mend0z0/SparkleSplashy/Hardware/v1_20230102/Released Files/Source Files/3D Parts/User Library-XFDFN-8E.step

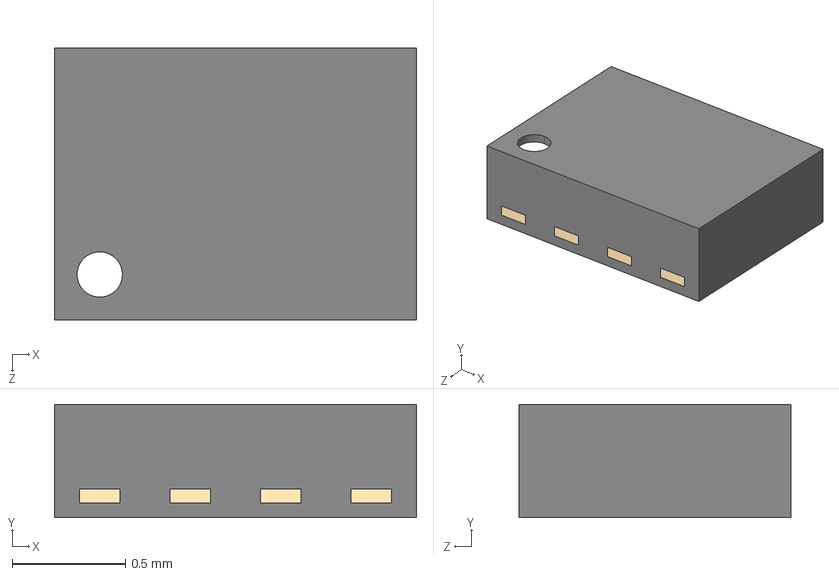
[picture p17: CAD file, 2023-09-30]
Hardware/v1_20230102/Released Files/Source Files/3D Parts/User Library-XFDFN-8E.step
1.60 x 0.5 x 1.20 mm
