mend0z0/SparkleSplashy/Hardware/v1_20230102/Design Files/_HW_SparkleSplashy/3D Parts/User Library-DO-214BA.step

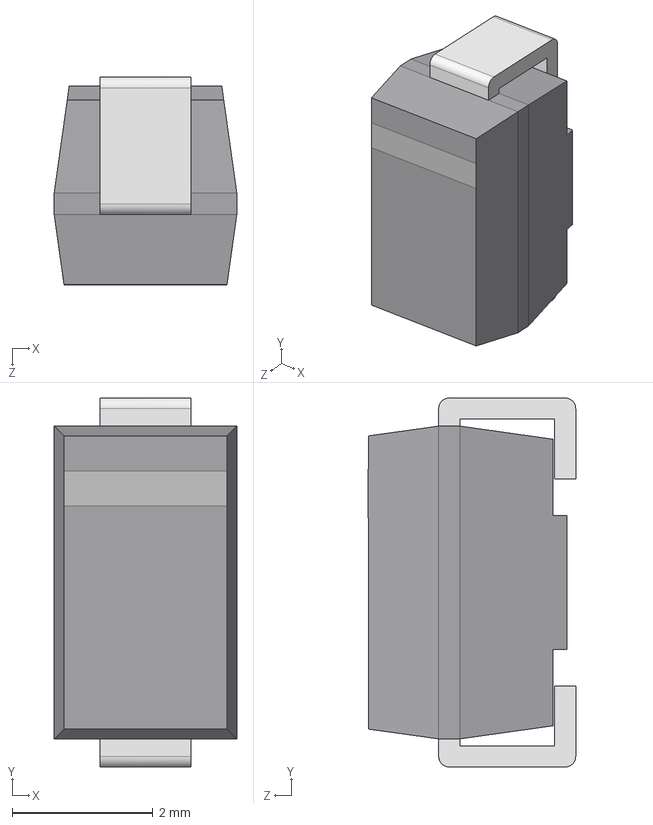
[picture p18: CAD file, 2023-09-30]
Hardware/v1_20230102/Design Files/_HW_SparkleSplashy/3D Parts/User Library-DO-214BA.step
2.60 x 5.25 x 2.95 mm
