mend0z0/SparkleSplashy/Hardware/v1_20230102/Released Files/Source Files/3D Parts/User Library-DFN-8 2x2.step

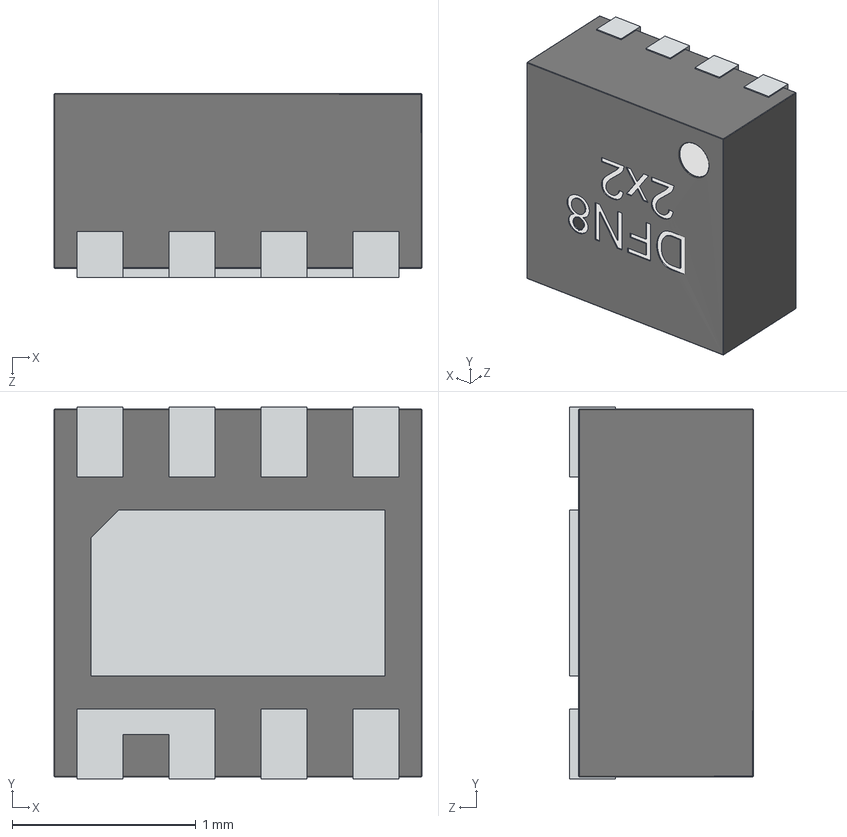
[picture p19: CAD file, 2023-09-30]
Hardware/v1_20230102/Released Files/Source Files/3D Parts/User Library-DFN-8 2x2.step
2.00 x 2.02 x 1.00 mm
