mend0z0/SparkleSplashy/Hardware/v1_20230102/Released Files/Source Files/3D Parts/User Library-CDRH3D23.step

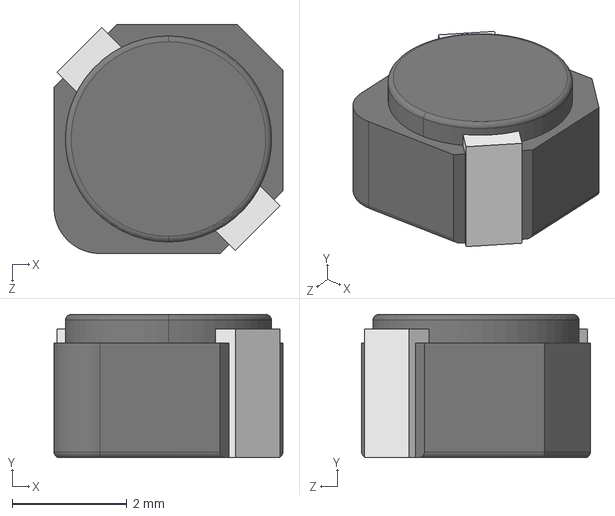
[picture p20: CAD file, 2023-09-30]
Hardware/v1_20230102/Released Files/Source Files/3D Parts/User Library-CDRH3D23.step
4.00 x 2.50 x 4.00 mm
