mend0z0/SparkleSplashy/Hardware/v1_20230102/Released Files/Source Files/3D Parts/User Library-FPC-40-2.step

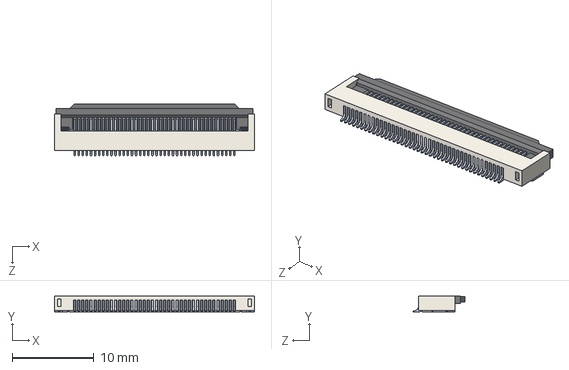
[picture p21: CAD file, 2023-09-30]
Hardware/v1_20230102/Released Files/Source Files/3D Parts/User Library-FPC-40-2.step
24.4 x 1.95 x 6.30 mm
