mend0z0/SparkleSplashy/Hardware/v1_20230102/Released Files/Source Files/3D Parts/PSON50P145X100X54-6N.step

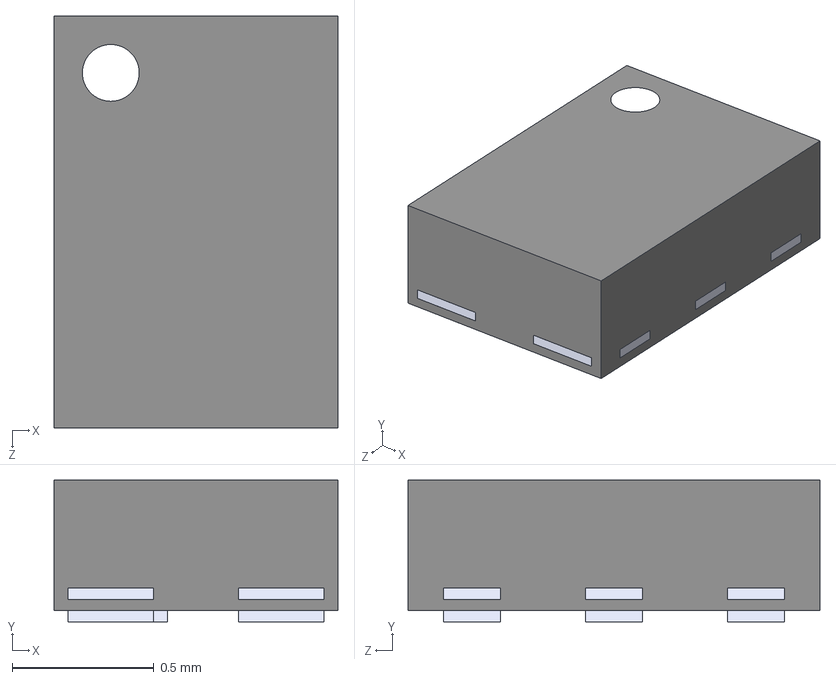
[picture p22: CAD file, 2023-09-30]
Hardware/v1_20230102/Released Files/Source Files/3D Parts/PSON50P145X100X54-6N.step
1.00 x 0.5 x 1.45 mm
