mend0z0/SparkleSplashy/Hardware/v1_20230102/Design Files/_HW_SparkleSplashy/3D Parts/LAN8720A-CP.step

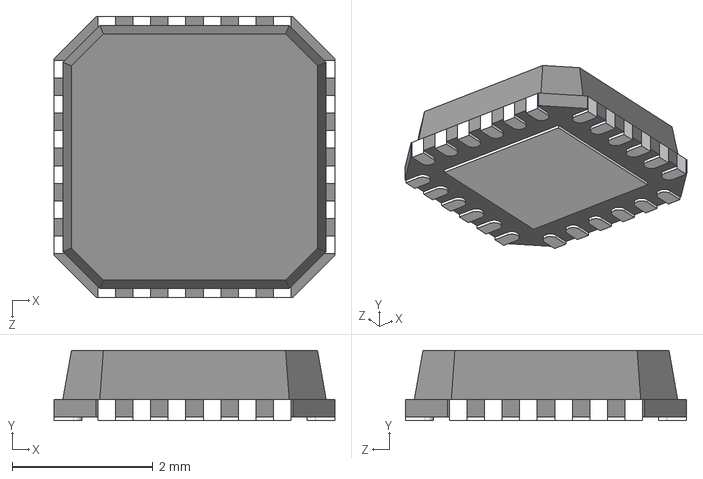
[picture p23: CAD file, 2023-09-30]
Hardware/v1_20230102/Design Files/_HW_SparkleSplashy/3D Parts/LAN8720A-CP.step
4.00 x 1 x 4.00 mm
