mend0z0/SparkleSplashy/Hardware/v1_20230102/Design Files/Design Guides/74LVC2G240_TRUTH-TABLE.png

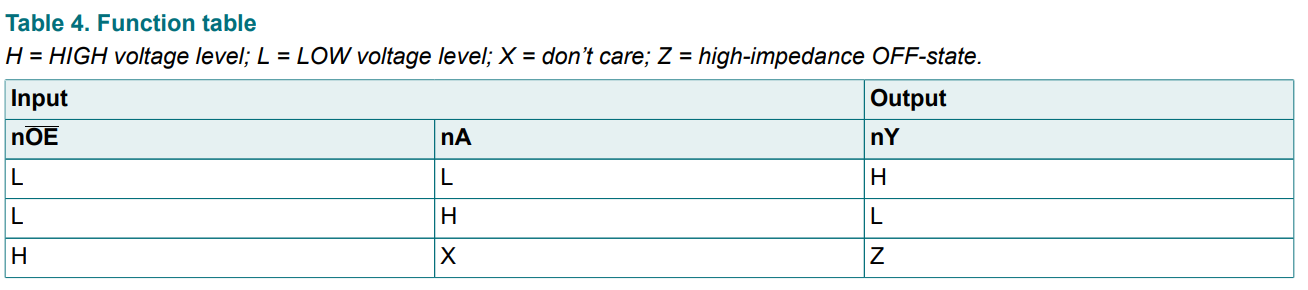
Hardware/v1_20230102/Design Files/Design Guides/74LVC2G240_TRUTH-TABLE.png
