mend0z0/SparkleSplashy/Hardware/v1_20230102/Design Files/Design Guides/adafruit_products_KeeBoar_sch.png

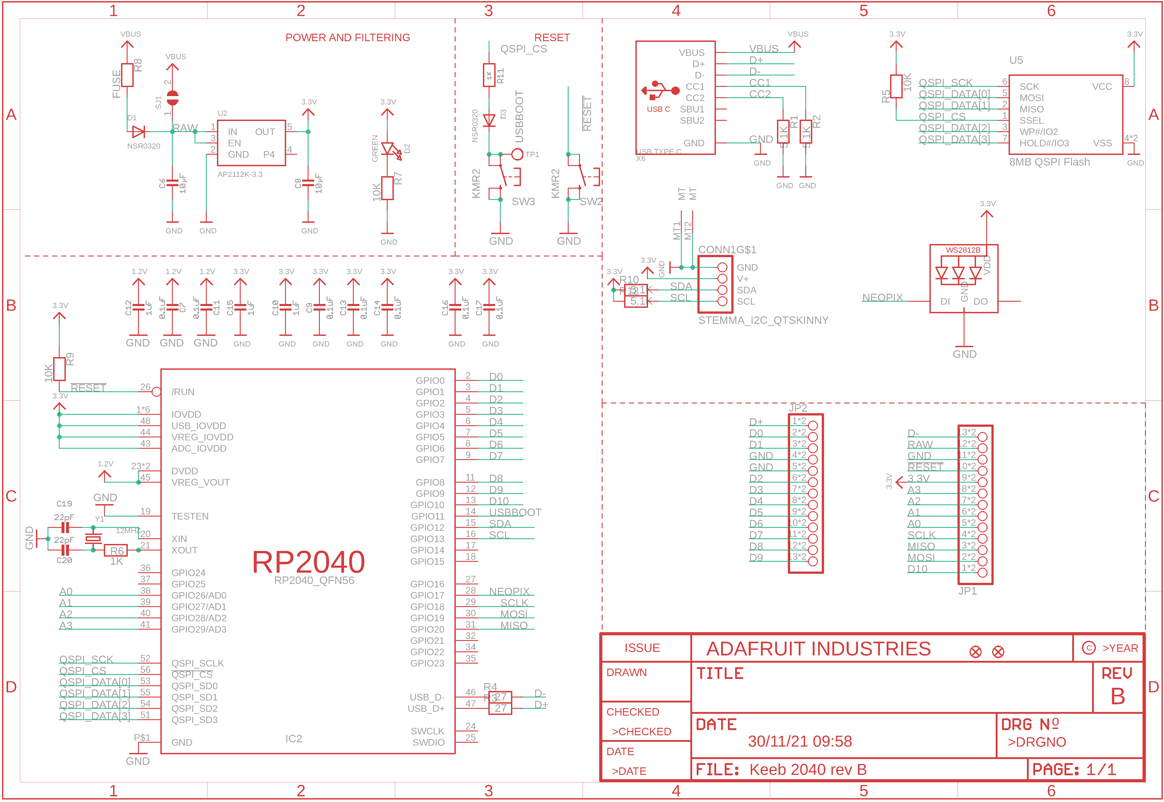
Hardware/v1_20230102/Design Files/Design Guides/adafruit_products_KeeBoar_sch.png
