mend0z0/SparkleSplashy/Hardware/v1_20230102/Design Files/Design Guides/Ethernet/GUID-9D7AC0DB-6FB3-4E10-80E7-3DFDD2FE818B-low.png

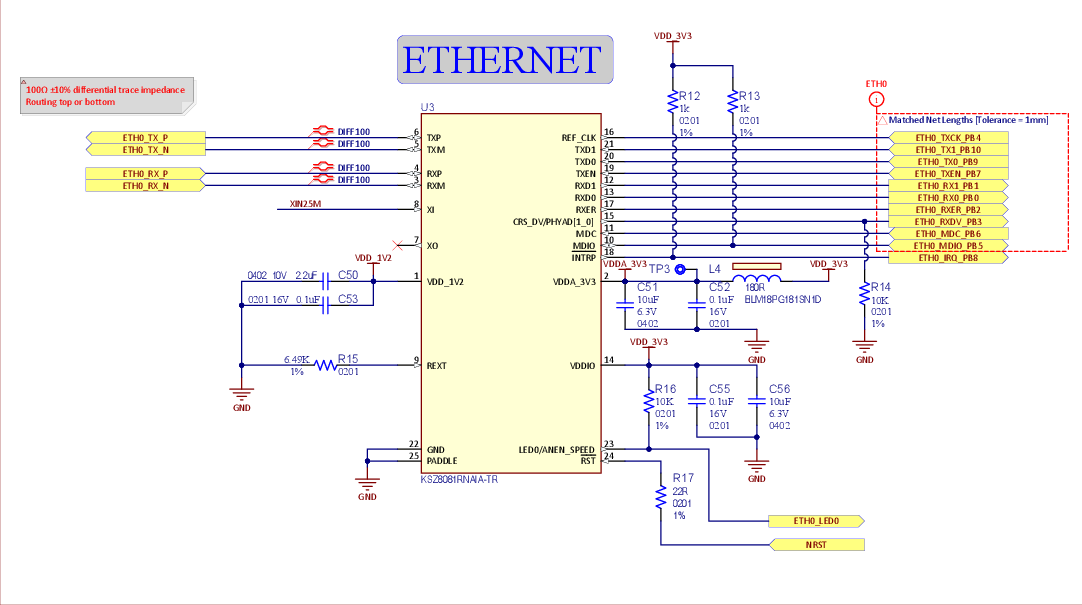
Hardware/v1_20230102/Design Files/Design Guides/Ethernet/GUID-9D7AC0DB-6FB3-4E10-80E7-3DFDD2FE818B-low.png
