mend0z0/SparkleSplashy/Hardware/v1_20230102/Design Files/Design Guides/Ethernet/Sans titre.png

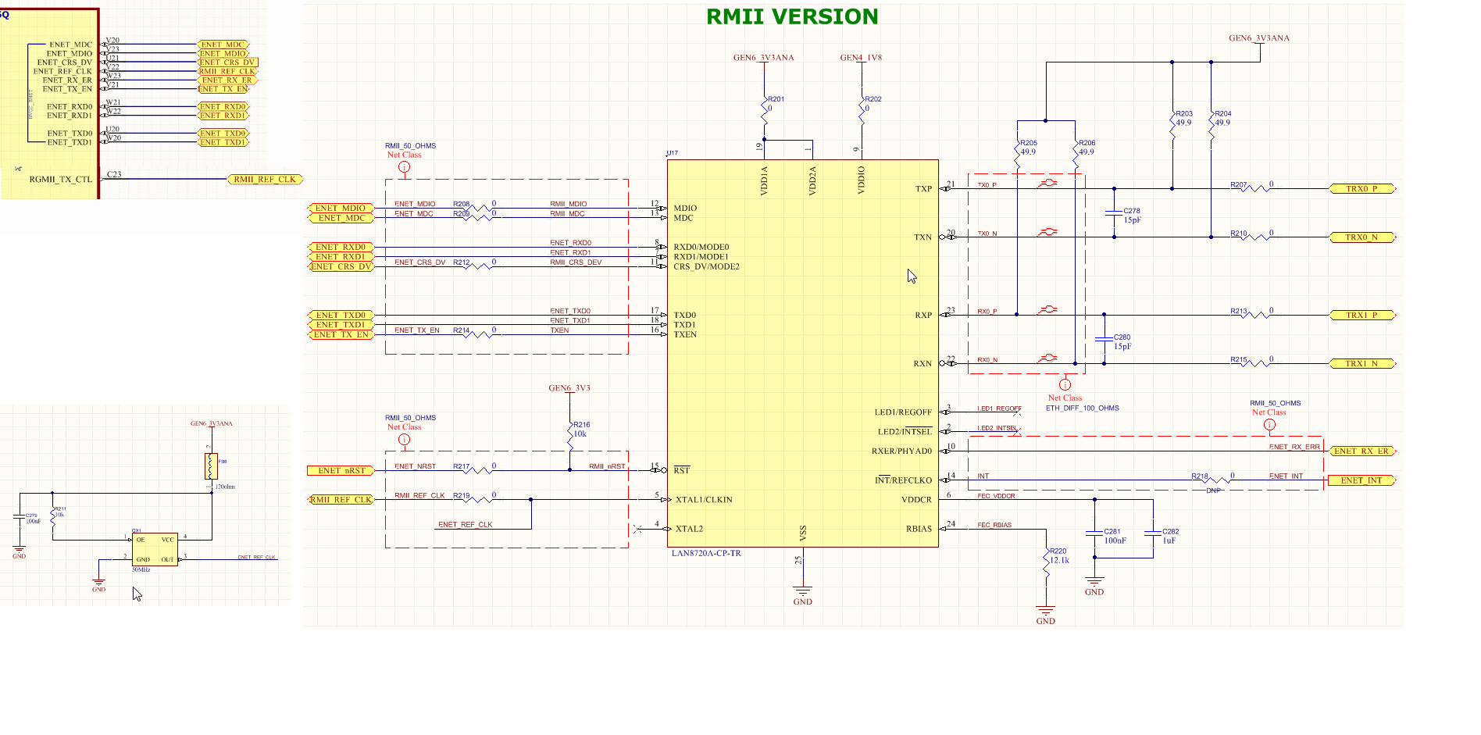
Hardware/v1_20230102/Design Files/Design Guides/Ethernet/Sans titre.png
