mend0z0/SparkleSplashy/Hardware/v1_20230102/Design Files/Design Guides/fusb302bvmpx_i2c_addr.png

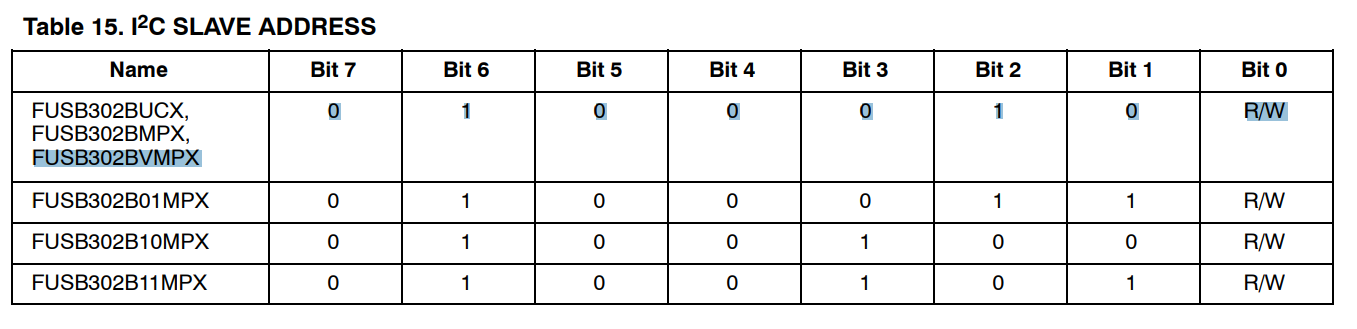
Hardware/v1_20230102/Design Files/Design Guides/fusb302bvmpx_i2c_addr.png
