mend0z0/SparkleSplashy/Hardware/v1_20230102/Design Files/Design Guides/ISO7720_LAYOUT.png

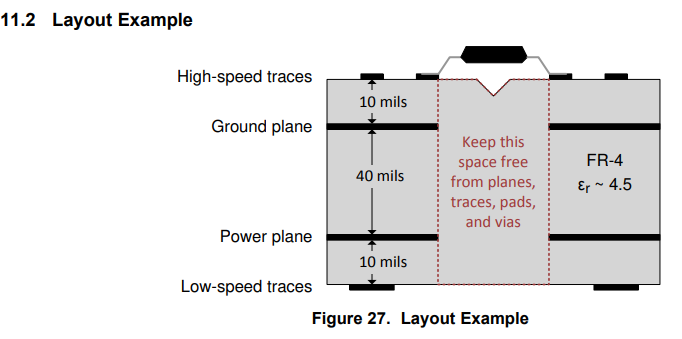
Hardware/v1_20230102/Design Files/Design Guides/ISO7720_LAYOUT.png
