mend0z0/SparkleSplashy/Hardware/v1_20230102/Design Files/Design Guides/MAX22028F_Typ App.png

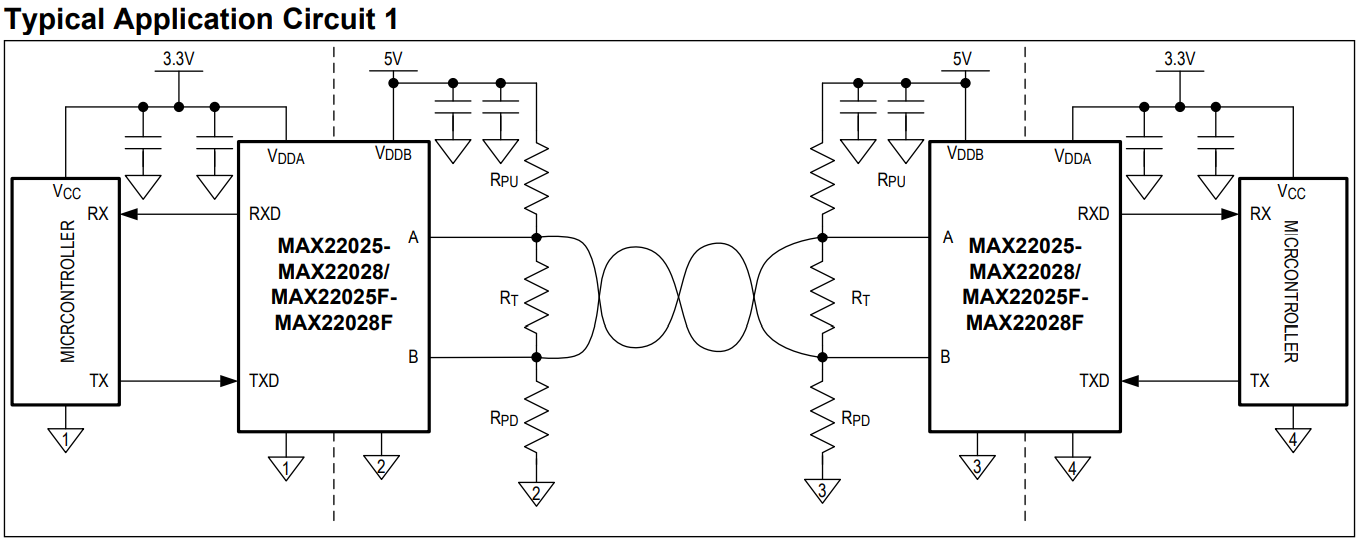
Hardware/v1_20230102/Design Files/Design Guides/MAX22028F_Typ App.png
