mend0z0/SparkleSplashy/Hardware/v1_20230102/Design Files/Design Guides/mic536_layout.png

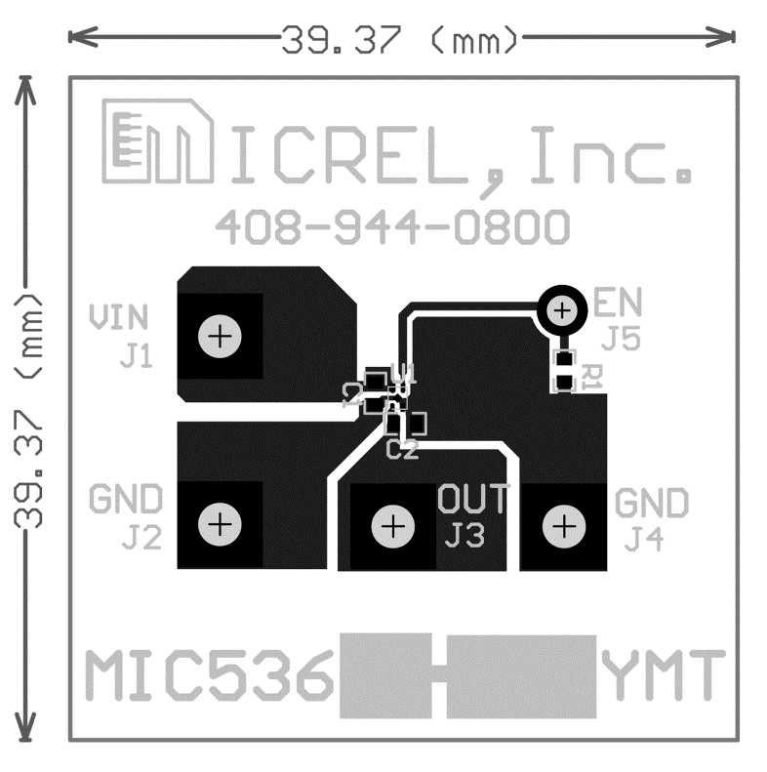
Hardware/v1_20230102/Design Files/Design Guides/mic536_layout.png
