mend0z0/SparkleSplashy/Hardware/v1_20230102/Design Files/Design Guides/RGB_Interface.png

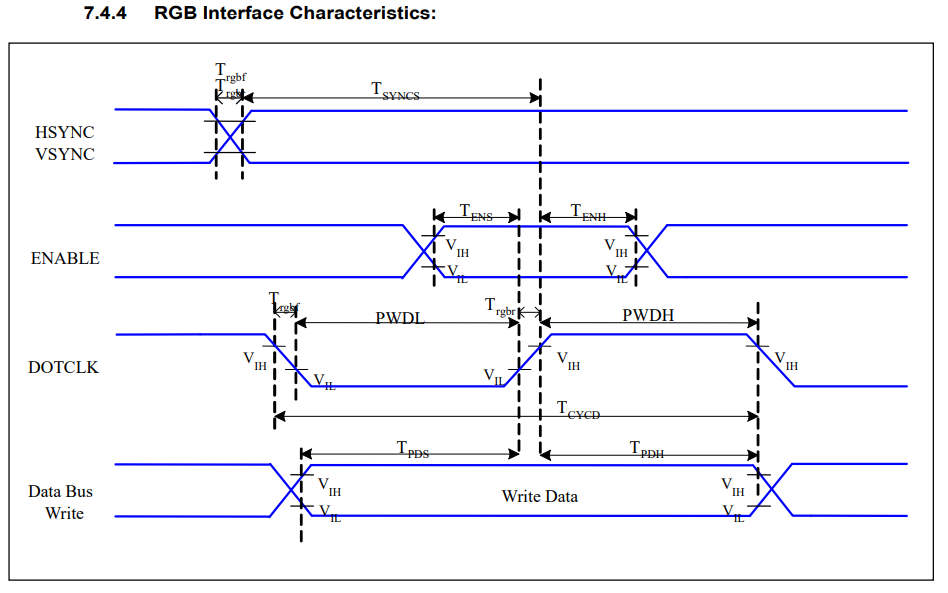
Hardware/v1_20230102/Design Files/Design Guides/RGB_Interface.png
