mend0z0/SparkleSplashy/Hardware/v1_20230102/Design Files/Design Guides/Screenshot 2023-01-23 070410.png

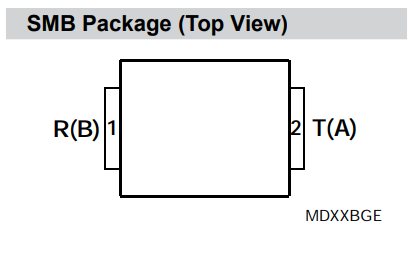
Hardware/v1_20230102/Design Files/Design Guides/Screenshot 2023-01-23 070410.png
