mend0z0/SparkleSplashy/Hardware/v1_20230102/Design Files/Design Guides/TFT_INTERFACE_SELECTION.png

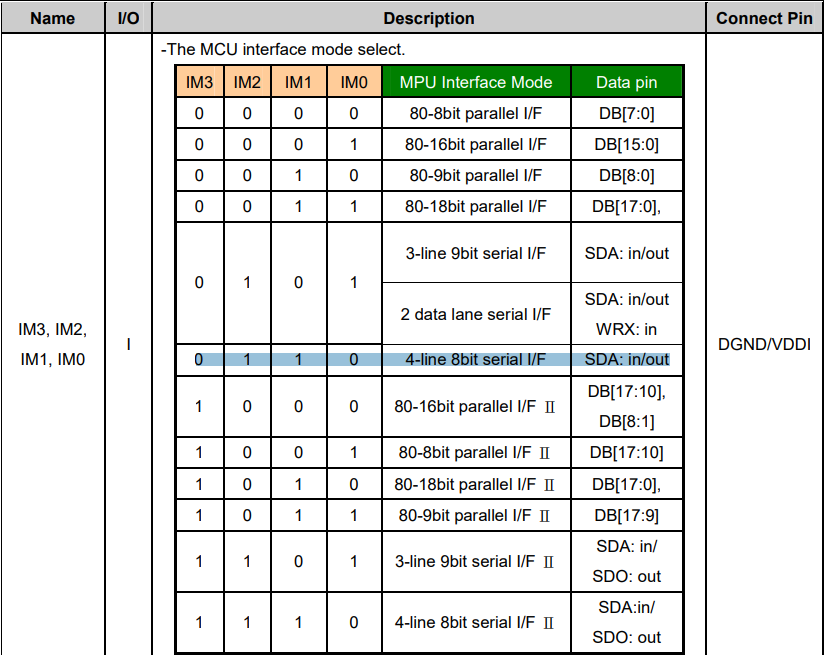
Hardware/v1_20230102/Design Files/Design Guides/TFT_INTERFACE_SELECTION.png
