mend0z0/SparkleSplashy/Hardware/v1_20230102/Design Files/Design Guides/USBC-UFP Rd.png

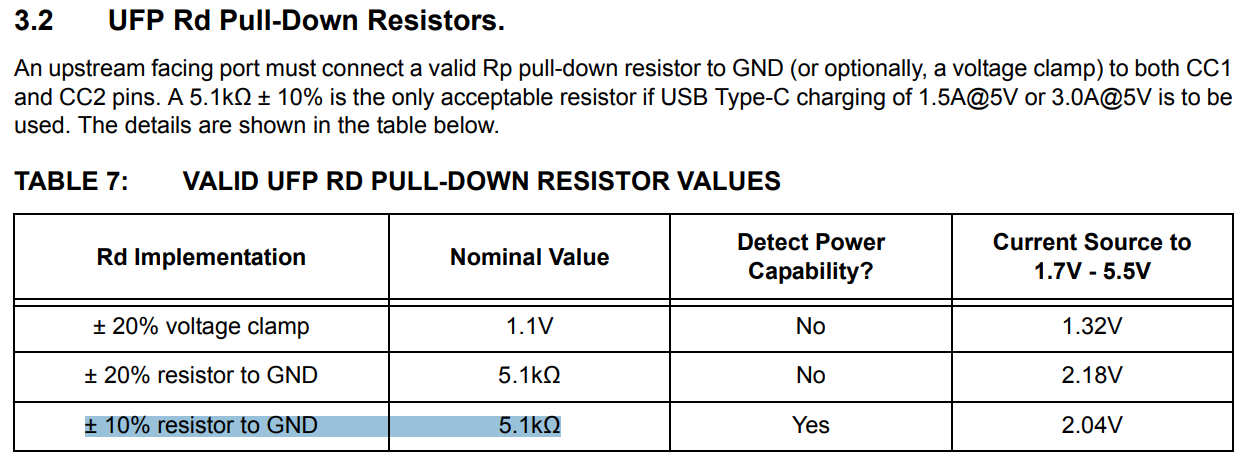
Hardware/v1_20230102/Design Files/Design Guides/USBC-UFP Rd.png
